eGuardianDev/GRVR/Firmware/Tests/ScoketTest/ScoketTest.ino

#include <Arduino.h>
#include <ESP8266WiFi.h>
#include <WiFiClient.h>

const uint16_t port = 5005;
const char *host = "192.168.0.103";
WiFiClient client;
void setup()
{
    Serial.begin(115200);
    Serial.println("Connecting...\n");
    WiFi.mode(WIFI_STA);
    WiFi.begin("", ""); // change it to your ussid and password
    while (WiFi.status() != WL_CONNECTED)
    {
        delay(500);
        Serial.print(".");
    }
}

void loop()
{
    if (!client.connect(host, port))
    {
        Serial.println("Connection to host failed");
        delay(1000);
        return;
    }
    Serial.println("Connected to server successful!");
    client.print("Hello From ESP8266");
   /* delay(10);
    while (client.available() > 0)
    {
        char c = client.read();
        Serial.write(c);
    }*/
    Serial.print('\n');
   //client.stop();
    delay(10);
}
